sini6a/phnx/assets/20240422_221215.jpg

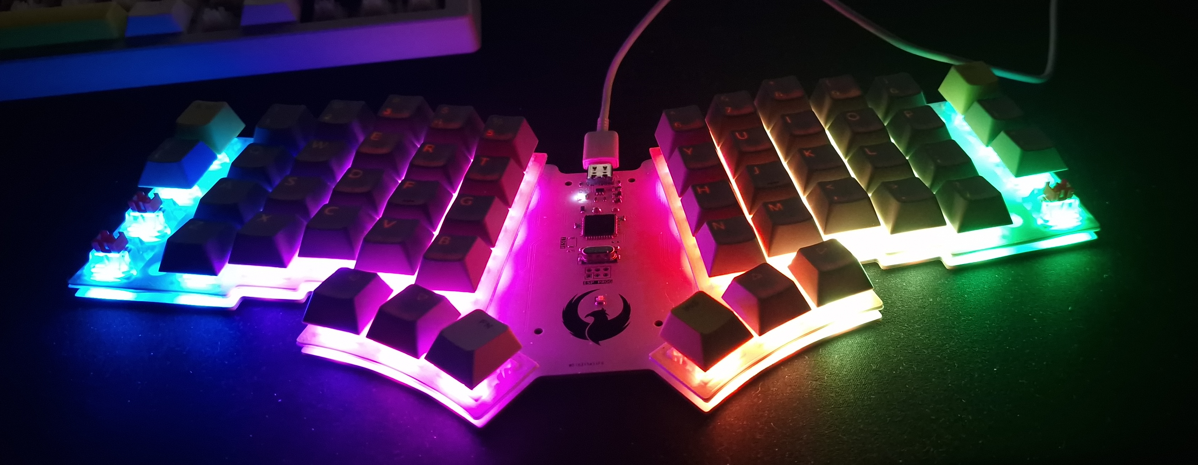
assets/20240422_221215.jpg
