sini6a/phnx/kicad/led.kicad_sch

## KiCad design kicad/led.kicad_sch (2024-04-28)

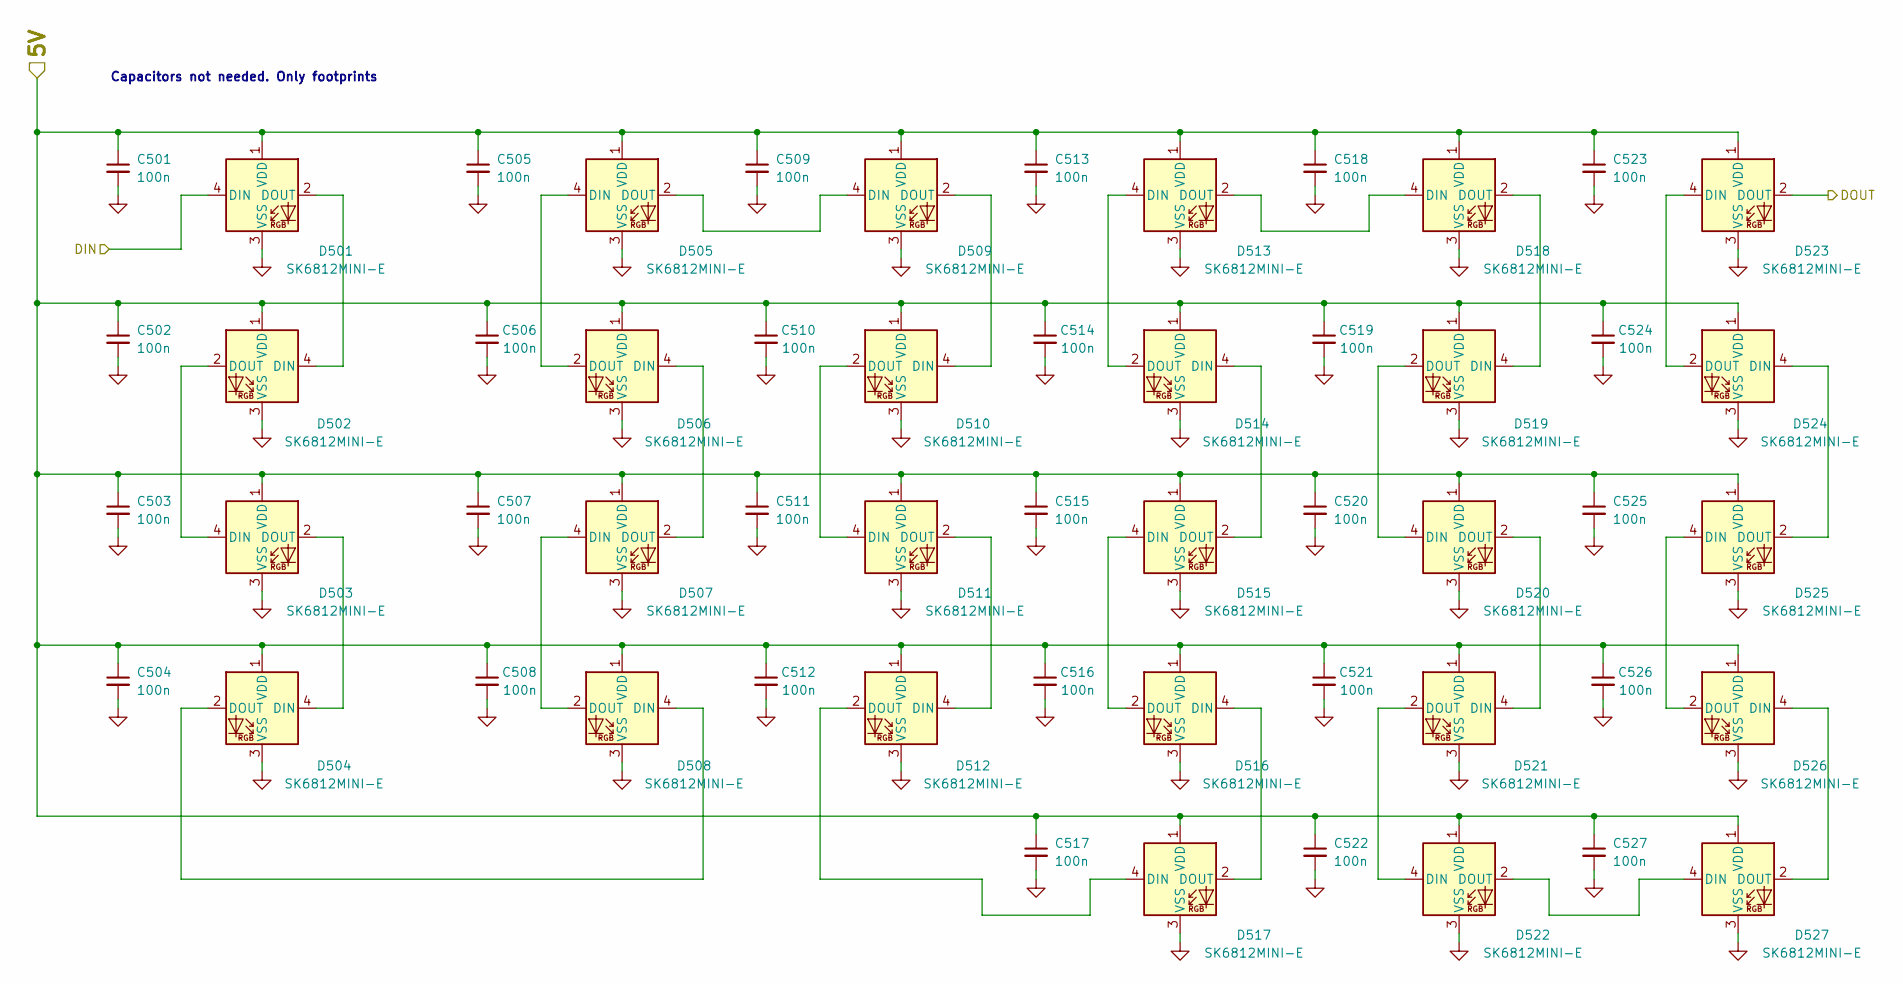
[picture p24: schematic led.kicad_sch]

Parts:
C501, C502, C503, C504, C505, C506, C507, C508, C509, C510, C511, C512, C513, C514, C515, C516, C517, C518, C519, C520, C521, C522, C523, C524, C525, C526, C527: 100n; C_0603_1608Metric
D501, D502, D503, D504, D505, D506, D507, D508, D509, D510, D511, D512, D513, D514, D515, D516, D517, D518, D519, D520, D521, D522, D523, D524, D525, D526, D527: SK6812MINI-E; LED_SK6812MINI-E_3.2x2.8mm_P1.5mm-INVERTED

Connections:
5V: C501.1, C502.1, C503.1, C504.1, C505.1, C506.1, C507.1, C508.1, C509.1, C510.1, C511.1, C512.1, C513.1, C514.1, C515.1, C516.1, C517.1, C518.1, C519.1, C520.1, C521.1, C522.1, C523.1, C524.1, C525.1, C526.1, C527.1, D501.1 (VDD), D502.1 (VDD), D503.1 (VDD), D504.1 (VDD), D505.1 (VDD), D506.1 (VDD), D507.1 (VDD), D508.1 (VDD), D509.1 (VDD), D510.1 (VDD), D511.1 (VDD), D512.1 (VDD), D513.1 (VDD), D514.1 (VDD), D515.1 (VDD), D516.1 (VDD), D517.1 (VDD), D518.1 (VDD), D519.1 (VDD), D520.1 (VDD), D521.1 (VDD), D522.1 (VDD), D523.1 (VDD), D524.1 (VDD), D525.1 (VDD), D526.1 (VDD), D527.1 (VDD)
DIN: D501.4 (DIN)
DOUT: D523.2 (DOUT)
GND: C501.2, C502.2, C503.2, C504.2, C505.2, C506.2, C507.2, C508.2, C509.2, C510.2, C511.2, C512.2, C513.2, C514.2, C515.2, C516.2, C517.2, C518.2, C519.2, C520.2, C521.2, C522.2, C523.2, C524.2, C525.2, C526.2, C527.2, D501.3 (VSS), D502.3 (VSS), D503.3 (VSS), D504.3 (VSS), D505.3 (VSS), D506.3 (VSS), D507.3 (VSS), D508.3 (VSS), D509.3 (VSS), D510.3 (VSS), D511.3 (VSS), D512.3 (VSS), D513.3 (VSS), D514.3 (VSS), D515.3 (VSS), D516.3 (VSS), D517.3 (VSS), D518.3 (VSS), D519.3 (VSS), D520.3 (VSS), D521.3 (VSS), D522.3 (VSS), D523.3 (VSS), D524.3 (VSS), D525.3 (VSS), D526.3 (VSS), D527.3 (VSS)
unnamed: D501.2 (DOUT), D502.4 (DIN)
unnamed: D502.2 (DOUT), D503.4 (DIN)
unnamed: D503.2 (DOUT), D504.4 (DIN)
unnamed: D504.2 (DOUT), D508.4 (DIN)
unnamed: D505.2 (DOUT), D509.4 (DIN)
unnamed: D505.4 (DIN), D506.2 (DOUT)
unnamed: D506.4 (DIN), D507.2 (DOUT)
unnamed: D507.4 (DIN), D508.2 (DOUT)
unnamed: D509.2 (DOUT), D510.4 (DIN)
unnamed: D510.2 (DOUT), D511.4 (DIN)
unnamed: D511.2 (DOUT), D512.4 (DIN)
unnamed: D512.2 (DOUT), D517.4 (DIN)
unnamed: D513.2 (DOUT), D518.4 (DIN)
unnamed: D513.4 (DIN), D514.2 (DOUT)
unnamed: D514.4 (DIN), D515.2 (DOUT)
unnamed: D515.4 (DIN), D516.2 (DOUT)
unnamed: D516.4 (DIN), D517.2 (DOUT)
unnamed: D518.2 (DOUT), D519.4 (DIN)
unnamed: D519.2 (DOUT), D520.4 (DIN)
unnamed: D520.2 (DOUT), D521.4 (DIN)
unnamed: D521.2 (DOUT), D522.4 (DIN)
unnamed: D522.2 (DOUT), D527.4 (DIN)
unnamed: D523.4 (DIN), D524.2 (DOUT)
unnamed: D524.4 (DIN), D525.2 (DOUT)
unnamed: D525.4 (DIN), D526.2 (DOUT)
unnamed: D526.4 (DIN), D527.2 (DOUT)

Notes on the sheet:
Capacitors not needed. Only footprints
