sini6a/phnx/kicad/led_right.kicad_sch

## KiCad design kicad/led_right.kicad_sch (2025-05-08)

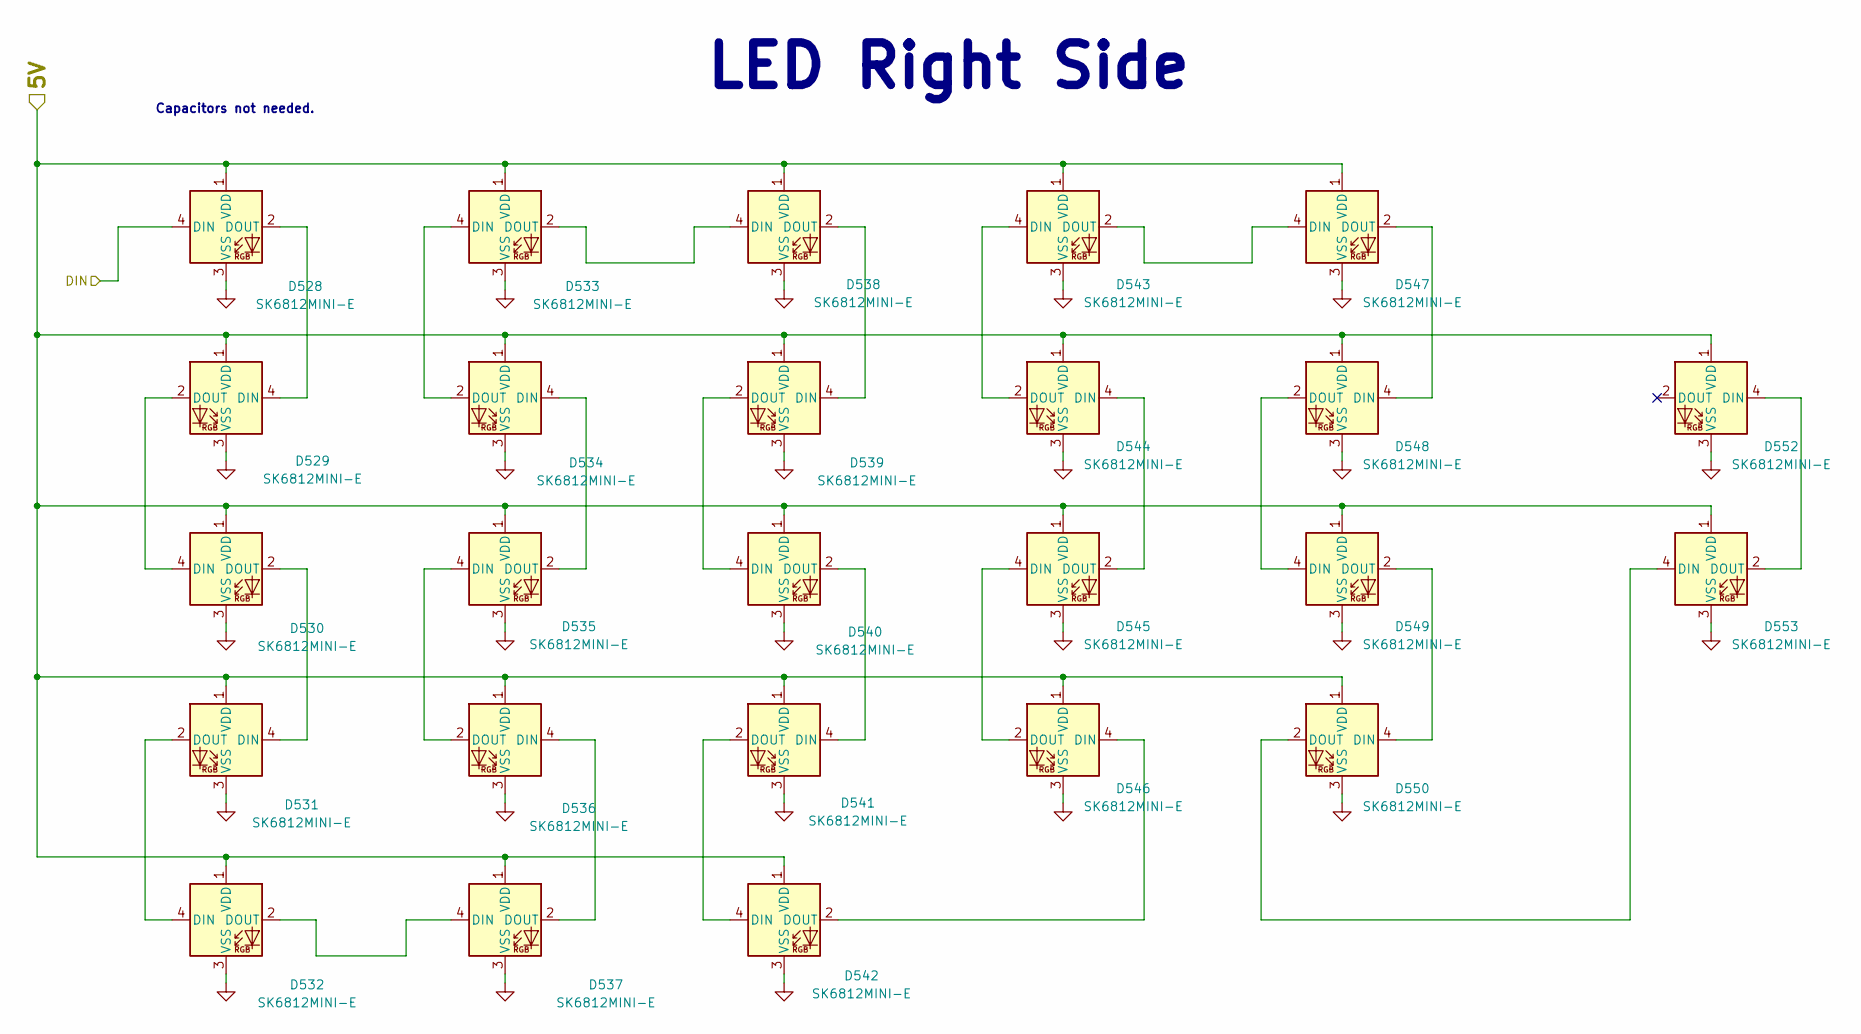
[picture p26: schematic led_right.kicad_sch]

Parts:
D528, D529, D530, D531, D532, D533, D534, D535, D536, D537, D538, D539, D540, D541, D542, D543, D544, D545, D546, D547, D548, D549, D550, D552, D553: SK6812MINI-E; LED_SK6812MINI-E_3.2x2.8mm_P1.5mm-INVERTED

Connections:
5V: D528.1 (VDD), D529.1 (VDD), D530.1 (VDD), D531.1 (VDD), D532.1 (VDD), D533.1 (VDD), D534.1 (VDD), D535.1 (VDD), D536.1 (VDD), D537.1 (VDD), D538.1 (VDD), D539.1 (VDD), D540.1 (VDD), D541.1 (VDD), D542.1 (VDD), D543.1 (VDD), D544.1 (VDD), D545.1 (VDD), D546.1 (VDD), D547.1 (VDD), D548.1 (VDD), D549.1 (VDD), D550.1 (VDD), D552.1 (VDD), D553.1 (VDD)
DIN: D528.4 (DIN)
GND: D528.3 (VSS), D529.3 (VSS), D530.3 (VSS), D531.3 (VSS), D532.3 (VSS), D533.3 (VSS), D534.3 (VSS), D535.3 (VSS), D536.3 (VSS), D537.3 (VSS), D538.3 (VSS), D539.3 (VSS), D540.3 (VSS), D541.3 (VSS), D542.3 (VSS), D543.3 (VSS), D544.3 (VSS), D545.3 (VSS), D546.3 (VSS), D547.3 (VSS), D548.3 (VSS), D549.3 (VSS), D550.3 (VSS), D552.3 (VSS), D553.3 (VSS)
unnamed: D528.2 (DOUT), D529.4 (DIN)
unnamed: D529.2 (DOUT), D530.4 (DIN)
unnamed: D530.2 (DOUT), D531.4 (DIN)
unnamed: D531.2 (DOUT), D532.4 (DIN)
unnamed: D532.2 (DOUT), D537.4 (DIN)
unnamed: D533.2 (DOUT), D538.4 (DIN)
unnamed: D533.4 (DIN), D534.2 (DOUT)
unnamed: D534.4 (DIN), D535.2 (DOUT)
unnamed: D535.4 (DIN), D536.2 (DOUT)
unnamed: D536.4 (DIN), D537.2 (DOUT)
unnamed: D538.2 (DOUT), D539.4 (DIN)
unnamed: D539.2 (DOUT), D540.4 (DIN)
unnamed: D540.2 (DOUT), D541.4 (DIN)
unnamed: D541.2 (DOUT), D542.4 (DIN)
unnamed: D542.2 (DOUT), D546.4 (DIN)
unnamed: D543.2 (DOUT), D547.4 (DIN)
unnamed: D543.4 (DIN), D544.2 (DOUT)
unnamed: D544.4 (DIN), D545.2 (DOUT)
unnamed: D545.4 (DIN), D546.2 (DOUT)
unnamed: D547.2 (DOUT), D548.4 (DIN)
unnamed: D548.2 (DOUT), D549.4 (DIN)
unnamed: D549.2 (DOUT), D550.4 (DIN)
unnamed: D550.2 (DOUT), D553.4 (DIN)
unnamed: D552.4 (DIN), D553.2 (DOUT)

Notes on the sheet:
LED Right Side
Capacitors not needed.
