sini6a/phnx/kicad/matrix.kicad_sch

## KiCad design kicad/matrix.kicad_sch (2025-05-08)

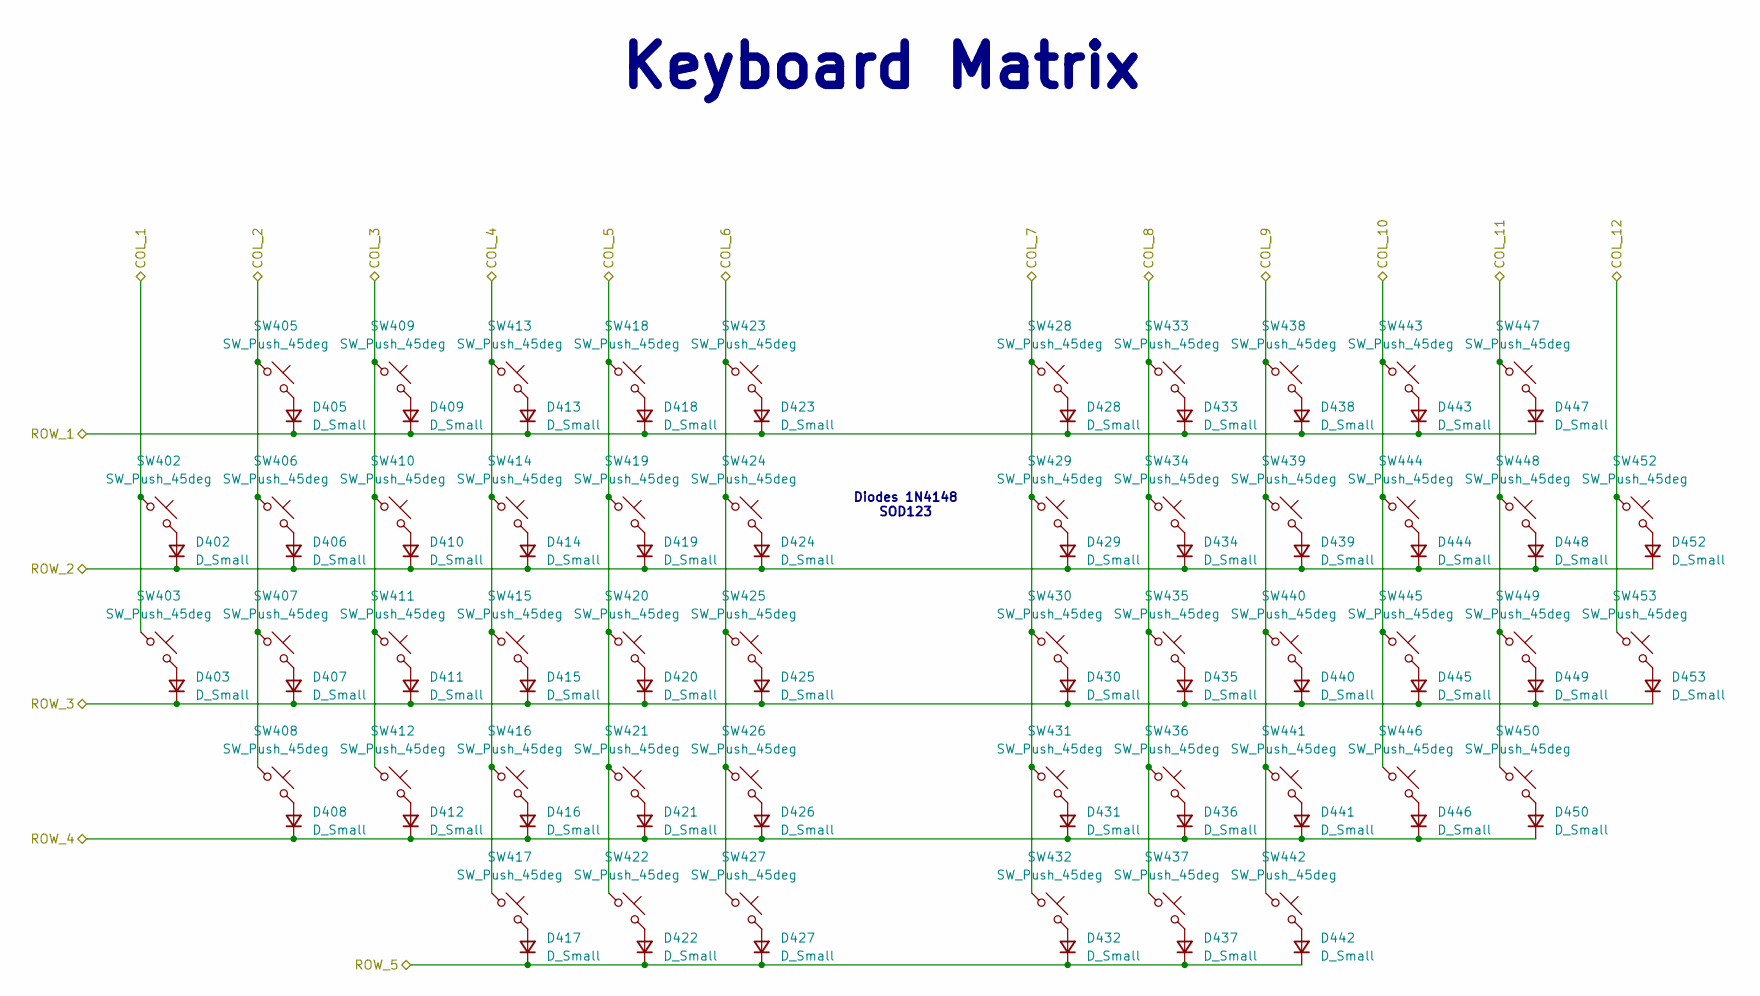
[picture p27: schematic matrix.kicad_sch]

Parts:
D402, D403, D405, D406, D407, D408, D409, D410, D411, D412, D413, D414, D415, D416, D417, D418, D419, D420, D421, D422, D423, D424, D425, D426, D427, D428, D429, D430, D431, D432, D433, D434, D435, D436, D437, D438, D439, D440, D441, D442, D443, D444, D445, D446, D447, D448, D449, D450, D452, D453: D_Small; D_SOD-123
SW402, SW403, SW405, SW406, SW407, SW408, SW409, SW410, SW411, SW412, SW413, SW414, SW415, SW416, SW417, SW418, SW419, SW420, SW421, SW422, SW423, SW424, SW425, SW426, SW427, SW428, SW429, SW430, SW431, SW432, SW433, SW434, SW435, SW436, SW437, SW438, SW439, SW440, SW441, SW442, SW443, SW444, SW445, SW446, SW447, SW448, SW449, SW450, SW452, SW453: SW_Push_45deg; SW_Cherry_MX_1.00u_PCB

Connections:
COL_1: SW402.1, SW403.1
COL_2: SW405.1, SW406.1, SW407.1, SW408.1
COL_3: SW409.1, SW410.1, SW411.1, SW412.1
COL_4: SW413.1, SW414.1, SW415.1, SW416.1, SW417.1
COL_5: SW418.1, SW419.1, SW420.1, SW421.1, SW422.1
COL_6: SW423.1, SW424.1, SW425.1, SW426.1, SW427.1
COL_7: SW428.1, SW429.1, SW430.1, SW431.1, SW432.1
COL_8: SW433.1, SW434.1, SW435.1, SW436.1, SW437.1
COL_9: SW438.1, SW439.1, SW440.1, SW441.1, SW442.1
COL_10: SW443.1, SW444.1, SW445.1, SW446.1
COL_11: SW447.1, SW448.1, SW449.1, SW450.1
COL_12: SW452.1, SW453.1
unnamed: D402.2 (A), SW402.2
unnamed: D403.2 (A), SW403.2
unnamed: D405.2 (A), SW405.2
unnamed: D406.2 (A), SW406.2
unnamed: D407.2 (A), SW407.2
unnamed: D408.2 (A), SW408.2
unnamed: D409.2 (A), SW409.2
unnamed: D410.2 (A), SW410.2
unnamed: D411.2 (A), SW411.2
unnamed: D412.2 (A), SW412.2
unnamed: D413.2 (A), SW413.2
unnamed: D414.2 (A), SW414.2
unnamed: D415.2 (A), SW415.2
unnamed: D416.2 (A), SW416.2
unnamed: D417.2 (A), SW417.2
unnamed: D418.2 (A), SW418.2
unnamed: D419.2 (A), SW419.2
unnamed: D420.2 (A), SW420.2
unnamed: D421.2 (A), SW421.2
unnamed: D422.2 (A), SW422.2
unnamed: D423.2 (A), SW423.2
unnamed: D424.2 (A), SW424.2
unnamed: D425.2 (A), SW425.2
unnamed: D426.2 (A), SW426.2
unnamed: D427.2 (A), SW427.2
unnamed: D428.2 (A), SW428.2
unnamed: D429.2 (A), SW429.2
unnamed: D430.2 (A), SW430.2
unnamed: D431.2 (A), SW431.2
unnamed: D432.2 (A), SW432.2
unnamed: D433.2 (A), SW433.2
unnamed: D434.2 (A), SW434.2
unnamed: D435.2 (A), SW435.2
unnamed: D436.2 (A), SW436.2
unnamed: D437.2 (A), SW437.2
unnamed: D438.2 (A), SW438.2
unnamed: D439.2 (A), SW439.2
unnamed: D440.2 (A), SW440.2
unnamed: D441.2 (A), SW441.2
unnamed: D442.2 (A), SW442.2
unnamed: D443.2 (A), SW443.2
unnamed: D444.2 (A), SW444.2
unnamed: D445.2 (A), SW445.2
unnamed: D446.2 (A), SW446.2
unnamed: D447.2 (A), SW447.2
unnamed: D448.2 (A), SW448.2
unnamed: D449.2 (A), SW449.2
unnamed: D450.2 (A), SW450.2
unnamed: D452.2 (A), SW452.2
unnamed: D453.2 (A), SW453.2
ROW_1: D405.1 (K), D409.1 (K), D413.1 (K), D418.1 (K), D423.1 (K), D428.1 (K), D433.1 (K), D438.1 (K), D443.1 (K), D447.1 (K)
ROW_2: D402.1 (K), D406.1 (K), D410.1 (K), D414.1 (K), D419.1 (K), D424.1 (K), D429.1 (K), D434.1 (K), D439.1 (K), D444.1 (K), D448.1 (K), D452.1 (K)
ROW_3: D403.1 (K), D407.1 (K), D411.1 (K), D415.1 (K), D420.1 (K), D425.1 (K), D430.1 (K), D435.1 (K), D440.1 (K), D445.1 (K), D449.1 (K), D453.1 (K)
ROW_4: D408.1 (K), D412.1 (K), D416.1 (K), D421.1 (K), D426.1 (K), D431.1 (K), D436.1 (K), D441.1 (K), D446.1 (K), D450.1 (K)
ROW_5: D417.1 (K), D422.1 (K), D427.1 (K), D432.1 (K), D437.1 (K), D442.1 (K)

Notes on the sheet:
Keyboard Matrix
Diodes 1N4148 SOD123
