sini6a/phnx/kicad/mcu.kicad_sch

## KiCad design kicad/mcu.kicad_sch (2025-05-08)

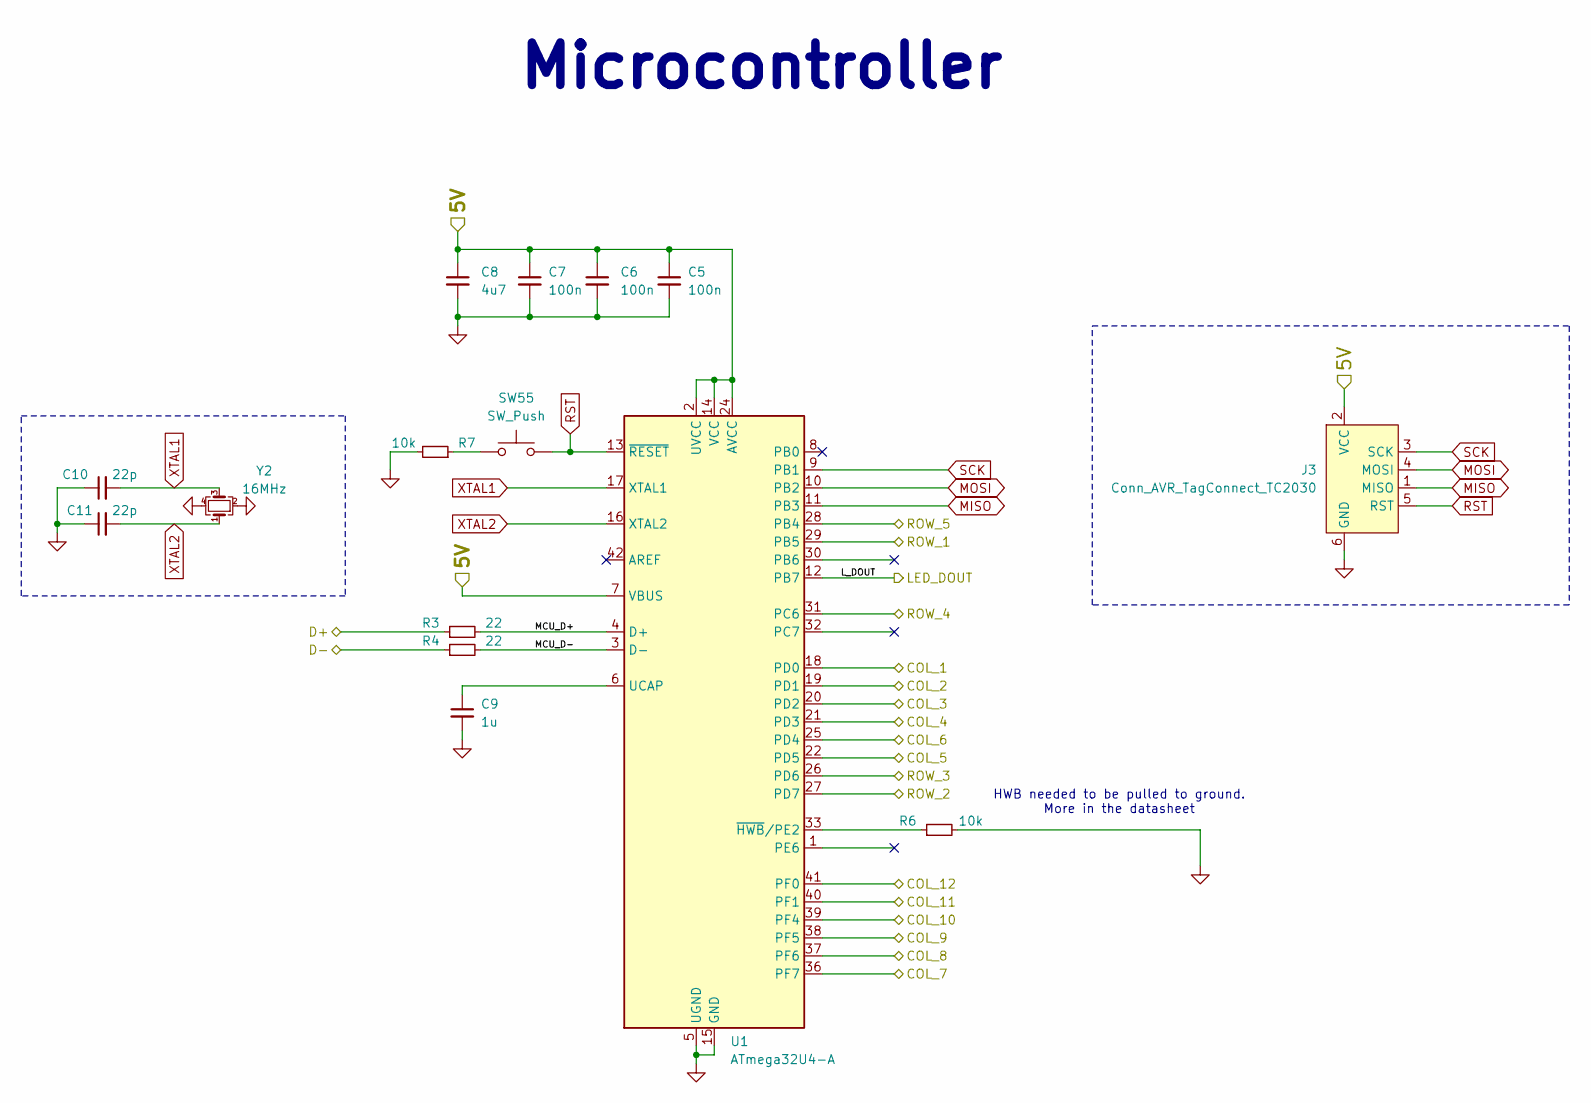
[picture p28: schematic mcu.kicad_sch]

Parts:
C5, C6, C7: 100n; C_0603_1608Metric
C8: 4u7; C_0805_2012Metric
C9: 1u; C_0805_2012Metric
C10, C11: 22p; C_0603_1608Metric
J3: Conn_AVR_TagConnect_TC2030; Tag-Connect_TC2030-IDC-NL_2x03_P1.27mm_Vertical
R3, R4: 22; R_0603_1608Metric
R6, R7: 10k; R_0603_1608Metric
SW55: SW_Push; SW_Push_SPST_NO_Alps_SKRK
U1: ATmega32U4-A; TQFP-44_10x10mm_P0.8mm
Y2: 16MHz; Crystal_SMD_3225-4Pin_3.2x2.5mm

Connections:
5V: C5.1, C6.1, C7.1, C8.1, J3.2 (VCC), U1.2 (UVCC), U1.7 (VBUS), U1.14 (VCC), U1.24 (AVCC), U1.34 (VCC), U1.44 (AVCC)
COL_1: U1.18 (PD0)
COL_2: U1.19 (PD1)
COL_3: U1.20 (PD2)
COL_4: U1.21 (PD3)
COL_5: U1.22 (PD5)
COL_6: U1.25 (PD4)
COL_7: U1.36 (PF7)
COL_8: U1.37 (PF6)
COL_9: U1.38 (PF5)
COL_10: U1.39 (PF4)
COL_11: U1.40 (PF1)
COL_12: U1.41 (PF0)
D+: R3.1
D-: R4.1
GND: C5.2, C6.2, C7.2, C8.2, C9.2, C10.1, C11.1, J3.6 (GND), R6.2, R7.2, U1.5 (UGND), U1.15 (GND), U1.23 (GND), U1.35 (GND), U1.43 (GND), Y2.2, Y2.4
L_DOUT: U1.12 (PB7)
MCU_D+: R3.2, U1.4 (D+)
MCU_D-: R4.2, U1.3 (D-)
MISO: J3.1 (MISO), U1.11 (PB3)
MOSI: J3.4 (MOSI), U1.10 (PB2)
unnamed: C9.1, U1.6 (UCAP)
unnamed: R6.1, U1.33 (~HWB/PE2)
unnamed: R7.1, SW55.2
ROW_1: U1.29 (PB5)
ROW_2: U1.27 (PD7)
ROW_3: U1.26 (PD6)
ROW_4: U1.31 (PC6)
ROW_5: U1.28 (PB4)
RST: J3.5 (RST), SW55.1, U1.13 (~RESET)
SCK: J3.3 (SCK), U1.9 (PB1)
XTAL1: C10.2, U1.17 (XTAL1), Y2.3
XTAL2: C11.2, U1.16 (XTAL2), Y2.1

Notes on the sheet:
Microcontroller
HWB needed to be pulled to ground. More in the datasheet
