sini6a/phnx/kicad/pdn.kicad_sch

## KiCad design kicad/pdn.kicad_sch (2025-05-08)

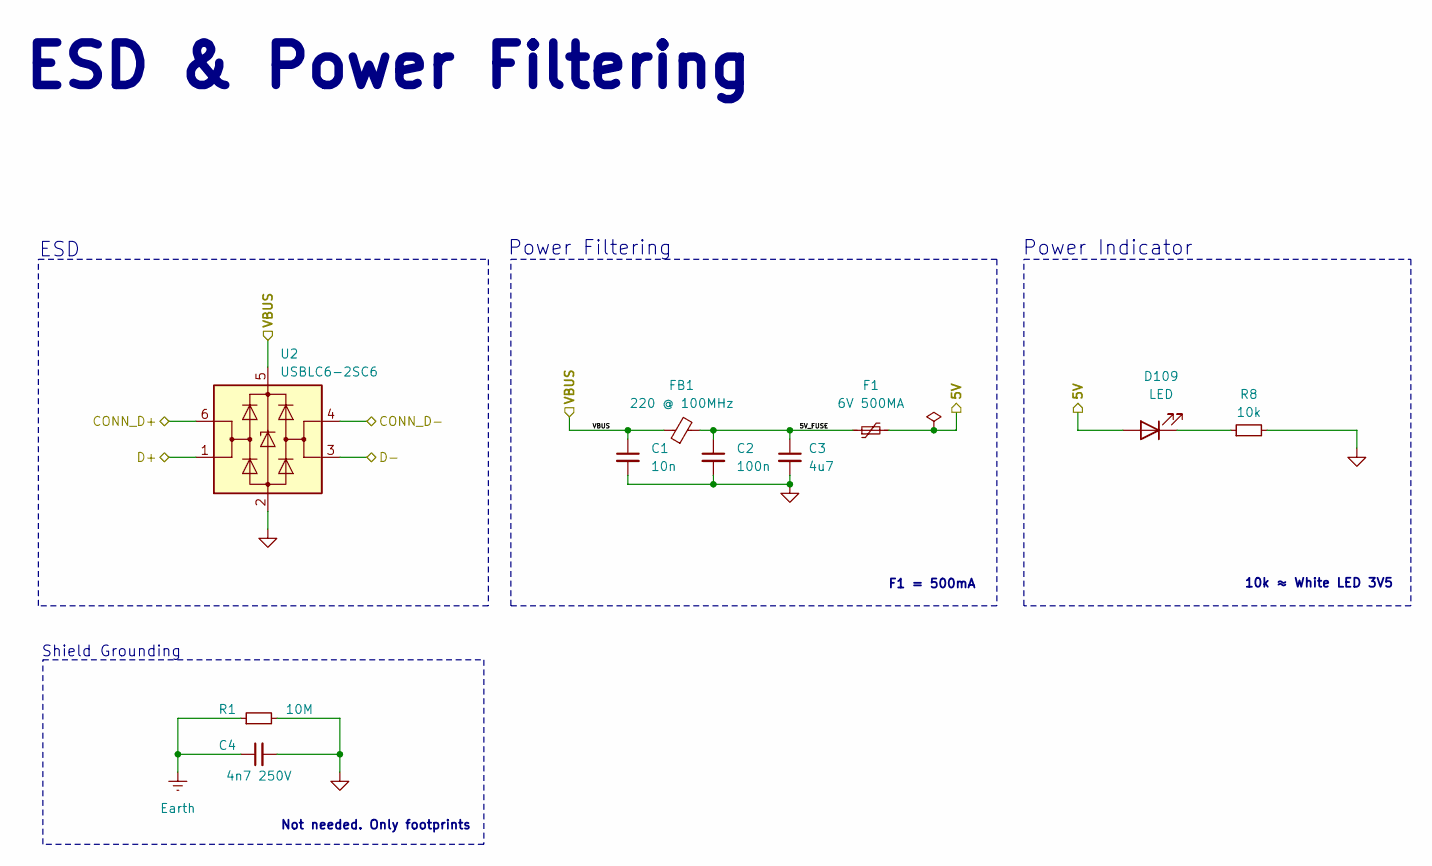
[picture p29: schematic pdn.kicad_sch]

Parts:
C1: 10n; C_0603_1608Metric
C2: 100n; C_0603_1608Metric
C3: 4u7; C_0805_2012Metric
C4: 4n7 250V; C_0603_1608Metric
D109: LED; LED_0805_2012Metric
F1: 6V 500MA; Fuse_0805_2012Metric
FB1: 220 @ 100MHz; L_0805_2012Metric
R1: 10M; R_0603_1608Metric
R8: 10k; R_0603_1608Metric
U2: USBLC6-2SC6; SOT-23-6

Connections:
5V: D109.2 (A), F1.2
5V_FUSE: C2.1, C3.1, F1.1, FB1.2
CONN_D+: U2.6 (I/O1)
CONN_D-: U2.4 (I/O2)
D+: U2.1 (I/O1)
D-: U2.3 (I/O2)
Earth: C4.1, R1.1
GND: C1.2, C2.2, C3.2, C4.2, R1.2, R8.2, U2.2 (GND)
unnamed: D109.1 (K), R8.1
VBUS: C1.1, FB1.1, U2.5 (VBUS)

Notes on the sheet:
ESD
F1 = 500mA
Not needed. Only footprints
ESD & Power Filtering
Power Indicator
Power Filtering
10k ≈ White LED 3V5
Shield Grounding
