sini6a/phnx/kicad/phnx.kicad_sch

## KiCad design kicad/phnx.kicad_sch (2025-05-08)

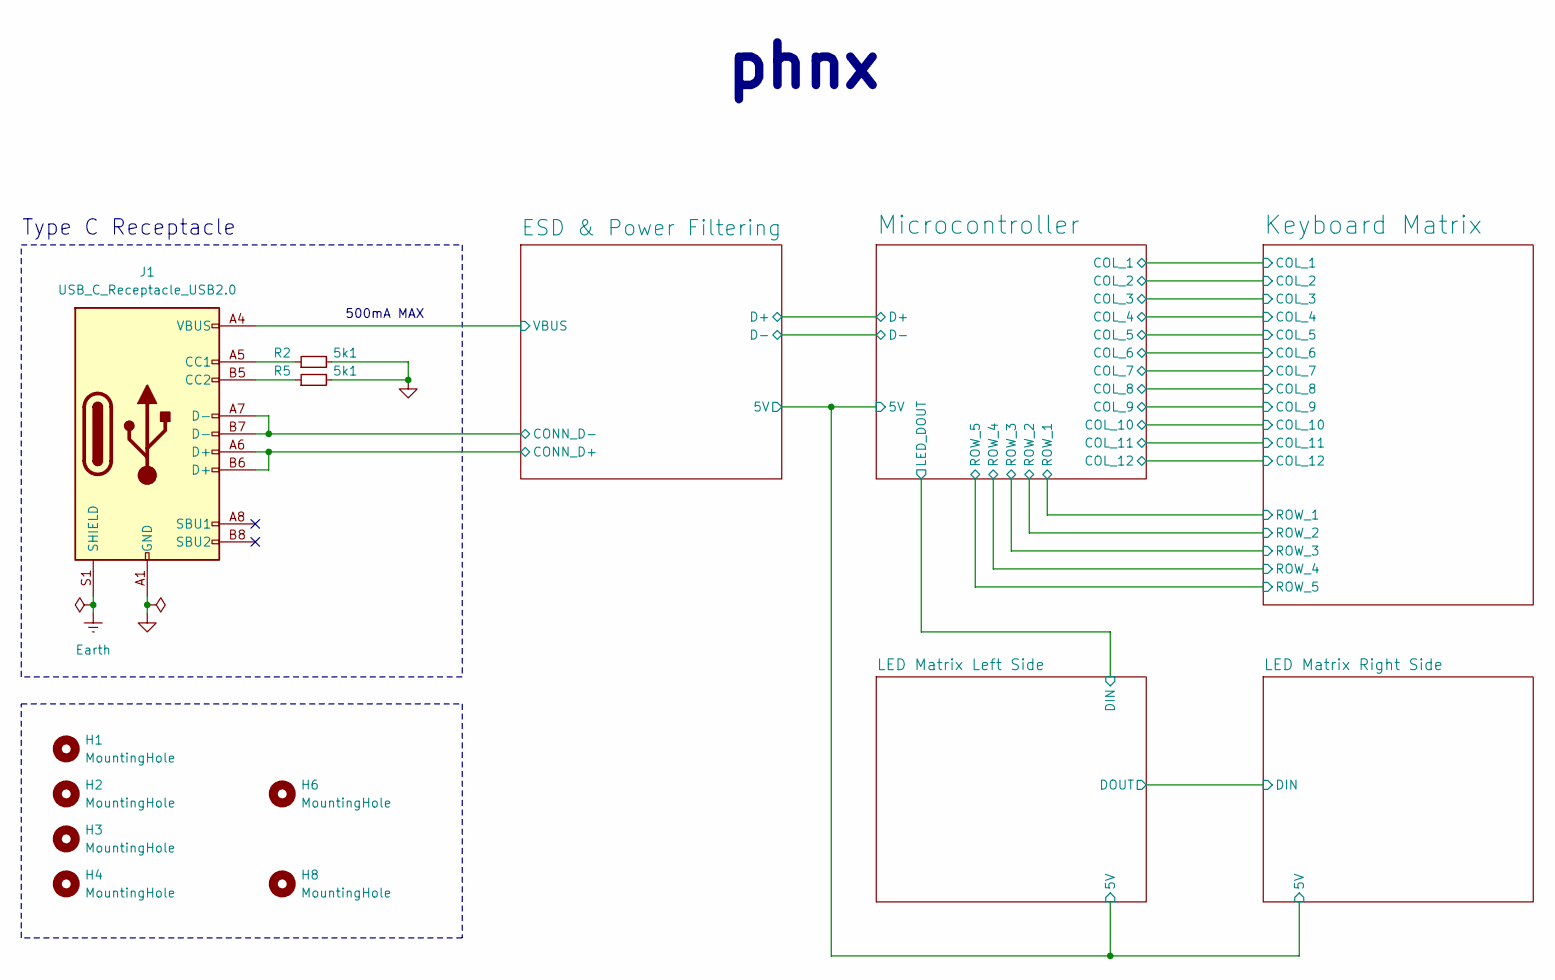
[picture p30: schematic phnx.kicad_sch]

Parts:
H1, H2, H3, H4, H6, H8: MountingHole; MountingHole_2.2mm_M2_ISO14580
J1: USB_C_Receptacle_USB2.0; USB_C_Receptacle_GCT_USB4105-xx-A_16P_TopMnt_Horizontal
R2, R5: 5k1; R_0603_1608Metric

Connections:
CONN_D+: J1.A6 (D+), J1.B6 (D+)
CONN_D-: J1.A7 (D-), J1.B7 (D-)
Earth: J1.S1 (SHIELD)
GND: J1.A1 (GND), J1.A12 (GND), J1.B1 (GND), J1.B12 (GND), R2.2, R5.2
unnamed: J1.A5 (CC1), R2.1
unnamed: J1.B5 (CC2), R5.1
VBUS: J1.A4 (VBUS), J1.A9 (VBUS), J1.B4 (VBUS), J1.B9 (VBUS)

Notes on the sheet:
Type C Receptacle
phnx
500mA MAX
